OxyMagnesium/scan-bv-logger/scan-bv-logger.kicad_sch

## KiCad design scan-bv-logger.kicad_sch (2022-04-13)

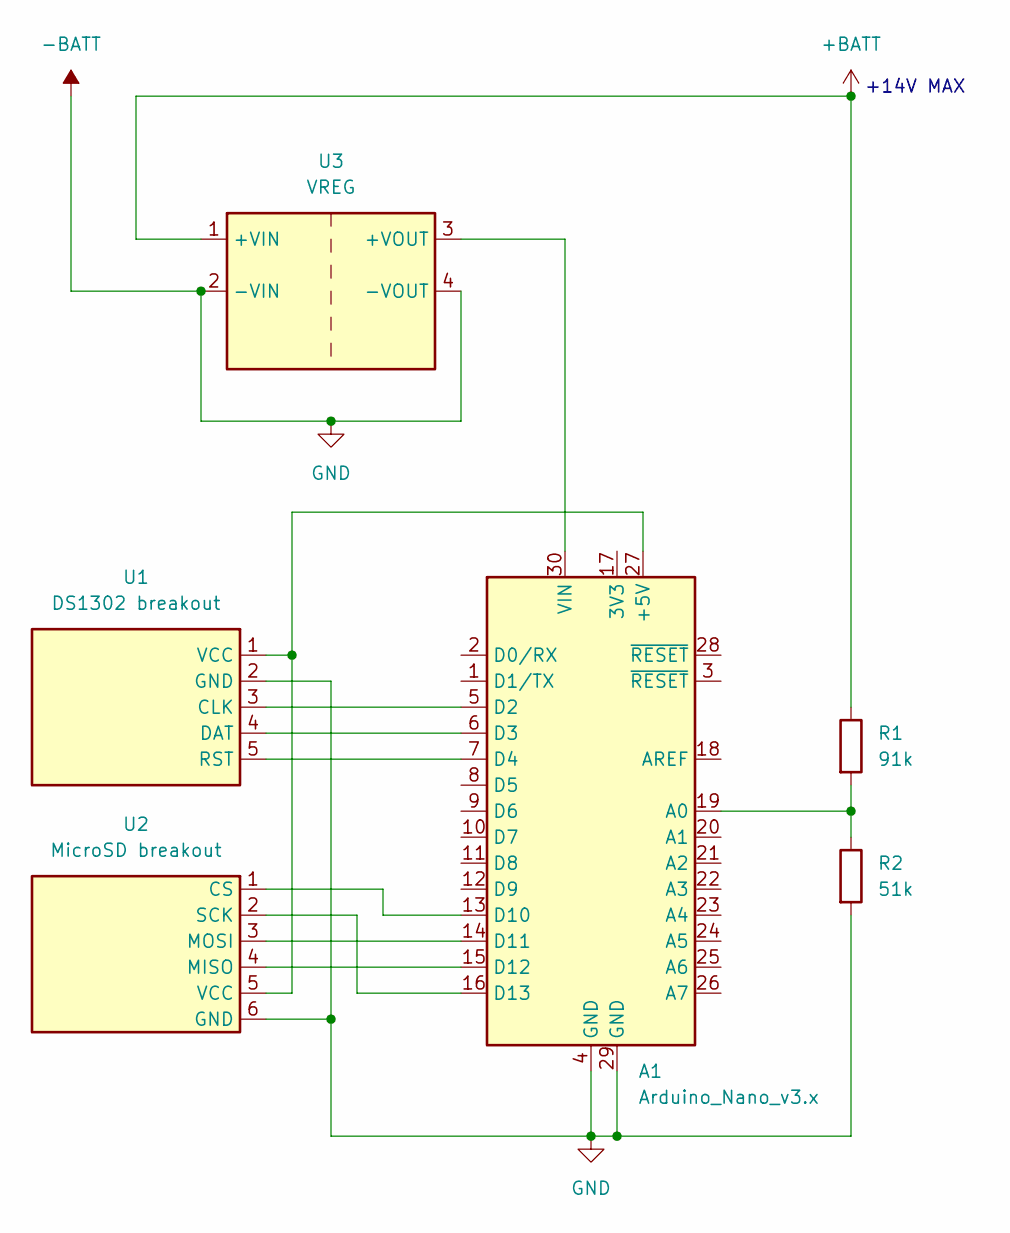
[picture p2: schematic scan-bv-logger.kicad_sch]

Parts:
A1: Arduino_Nano_v3.x; Arduino_Nano
R1: 91k
R2: 51k
U1: DS1302 breakout; DIP-8_W7.62mm
U2: MicroSD breakout; DIP-8_W7.62mm
U3: VREG; Converter_DCDC_XP_POWER-ISU02_SMD

Connections:
+BATT: R1.1, U3.1 (+VIN)
GND: A1.4 (GND), A1.29 (GND), R2.2, U1.2 (GND), U2.6 (GND), U3.2 (-VIN), U3.4 (-VOUT)
unnamed: A1.5 (D2), U1.3 (CLK)
unnamed: A1.6 (D3), U1.4 (DAT)
unnamed: A1.7 (D4), U1.5 (RST)
unnamed: A1.13 (D10), U2.1 (CS)
unnamed: A1.14 (D11), U2.3 (MOSI)
unnamed: A1.15 (D12), U2.4 (MISO)
unnamed: A1.16 (D13), U2.2 (SCK)
unnamed: A1.19 (A0), R1.2, R2.1
unnamed: A1.27 (+5V), U1.1 (VCC), U2.5 (VCC)
unnamed: A1.30 (VIN), U3.3 (+VOUT)

Notes on the sheet:
+14V MAX
